nradulovic/hw_minima/minima_amp/spice_minima/lm_ac.asc

C1: cap; {1/(2*pi*fp1)}
C2: cap; {1/(2*pi*fp2)}
C3: cap; {1/(2*pi*fp3)}
C4: cap; {1/(2*pi*fp4)}
C5: cap; 100n
C6: cap; 15p
C7: cap; 100n
C8: cap; 18p
E1: e; {10**(aol/20)}
E2: e; 1
E3: e; 1
E4: e; 1
E5: e; 1
Ii: current; 0; AC {u(prb)}
L1: ind; 5µ
R1: res; 1
R2: res; 1
R3: res; 499
R4: res; 1
R5: res; 499
R6: res; 2.7
R7: res; 7k5
R8: res; 1
R10: res; {rops}
R12: res; 499
R13: res; 2.7
R14: res; 8
R15: res; 1
R16: res; 4.7
R17: res; 7k5
V1: voltage; 0
V2: voltage; 0
V3: voltage; 15
V4: voltage; -15
Vgen: voltage; PULSE(0 1 1u 1n 1n 5u 10u)
Vi: voltage; 0; AC {u(-prb)}
Named nets: 0, in, x, xp, AC1, AC2, vcc, vee
.tran 10m
.ac oct 10 100 10meg
AC sonda
.step param prb list -1 1
.param aol=115
.param fp1=15
.param fp2=1.7meg
.param fp3=9e6
.param fp4=10e6
.param rf 8k
.param rg=500
.param prb=0
.param rops=240m
