nradulovic/hw_minima/minima_amp/spice_minima/lm_parallel.asc

C1: cap; 220p
L1: ind; 500µ; Rser=5
L2: ind; 500µ; Rser=5
L3: ind; 500µ; Rser=5
L4: ind; 500µ; Rser=5
L5: ind; 4m; Rser=5
R1: res; {510k*0.999}
R2: res; {510k*0.999}
R3: res; 330
R4: res; {510k*0.999}
R5: res; {510k*1.001}
R6: res; 330
R7: res; 80k
R8: res; {8.2e6*1.001}
R9: res; 330
R10: res; {8.2e6*0.999}
R11: res; 2k7
R12: res; 330
R13: res; 2k
R14: res; {8.2e6*1.001}
R15: res; {8.2e6*1.001}
U1: UniversalOpamp2; Avol=500k GBW=8Meg Slew=10Meg
U2: UniversalOpamp2; Avol=500k GBW=8Meg Slew=10Meg
U3: UniversalOpamp2; Avol=500k GBW=8Meg Slew=10Meg
U4: UniversalOpamp2; Avol=500k GBW=8Meg Slew=10Meg
V1: voltage; SINE(0 {30/((8.2/.51)+1)} 1k)
V2: voltage; 33
V3: voltage; -33
Named nets: 0, vcc, vee
.tran 10m
