nradulovic/hw_minima/minima_psu/spice_minima/dc_detect.asc

V1: voltage
V2: voltage
Named nets: 0, acp, acn
